engicoder/kroy360_usb/firmware/6x8_horizontal_lsb_1.h

#include <stdint.h>
#include <avr/pgmspace.h>

const uint8_t font[256][8] PROGMEM =
{
{0x00,0x00,0x00,0x00,0x00,0x00,0x00,0x00},	// 0x00
{0x70,0x88,0xD8,0x88,0xA8,0x88,0x70,0x00},	// 0x01
{0x70,0xF8,0xA8,0xF8,0x88,0xF8,0x70,0x00},	// 0x02
{0x00,0x50,0xF8,0xF8,0xF8,0x70,0x20,0x00},	// 0x03
{0x00,0x20,0x70,0xF8,0xF8,0x70,0x20,0x00},	// 0x04
{0x20,0x70,0x70,0x20,0xF8,0xF8,0x20,0x00},	// 0x05
{0x00,0x20,0x70,0xF8,0xF8,0x20,0x70,0x00},	// 0x06
{0x00,0x00,0x00,0x00,0x00,0x00,0x00,0x00},	// 0x07
{0x00,0x00,0x00,0x00,0x00,0x00,0x00,0x00},	// 0x08
{0x00,0x00,0x00,0x00,0x00,0x00,0x00,0x00},	// 0x09
{0x00,0x00,0x00,0x00,0x00,0x00,0x00,0x00},	// 0x0A
{0x00,0xE0,0xC0,0xB0,0x48,0x48,0x30,0x00},	// 0x0B
{0x70,0x88,0x88,0x70,0x20,0x70,0x20,0x00},	// 0x0C
{0x00,0x00,0x00,0x00,0x00,0x00,0x00,0x00},	// 0x0D
{0xC0,0xB0,0xD0,0xB0,0xD0,0xD8,0x18,0x00},	// 0x0E
{0x00,0xA8,0x70,0xD8,0x70,0xA8,0x00,0x00},	// 0x0F
{0x10,0x30,0x70,0xF0,0x70,0x30,0x10,0x00},	// 0x10
{0x40,0x60,0x70,0x78,0x70,0x60,0x40,0x00},	// 0x11
{0x20,0x70,0xF8,0x20,0xF8,0x70,0x20,0x00},	// 0x12
{0x50,0x50,0x50,0x50,0x50,0x00,0x50,0x00},	// 0x13
{0xF0,0xA8,0xA8,0xB0,0xA0,0xA0,0xA0,0x00},	// 0x14
{0x70,0x88,0x30,0x50,0x60,0x88,0x70,0x00},	// 0x15
{0x00,0x00,0x00,0x00,0x00,0x78,0x78,0x00},	// 0x16
{0x20,0x70,0xF8,0x20,0xF8,0x70,0x20,0x70},	// 0x17
{0x20,0x70,0xF8,0x20,0x20,0x20,0x20,0x00},	// 0x18
{0x20,0x20,0x20,0x20,0xF8,0x70,0x20,0x00},	// 0x19
{0x00,0x20,0x60,0xF8,0x60,0x20,0x00,0x00},	// 0x1A
{0x00,0x20,0x30,0xF8,0x30,0x20,0x00,0x00},	// 0x1B
{0x00,0x00,0x00,0x08,0x08,0x08,0xF8,0x00},	// 0x1C
{0x00,0x50,0x50,0xF8,0x50,0x50,0x00,0x00},	// 0x1D
{0x20,0x20,0x70,0x70,0xF8,0xF8,0x00,0x00},	// 0x1E
{0xF8,0xF8,0x70,0x70,0x20,0x20,0x00,0x00},	// 0x1F
{0x00,0x00,0x00,0x00,0x00,0x00,0x00,0x00},	// 0x20
{0x20,0x70,0x70,0x20,0x20,0x00,0x20,0x00},	// 0x21
{0xD8,0xD8,0x48,0x00,0x00,0x00,0x00,0x00},	// 0x22
{0x00,0x50,0xF8,0x50,0x50,0xF8,0x50,0x00},	// 0x23
{0x10,0x70,0x08,0x30,0x40,0x38,0x20,0x00},	// 0x24
{0x98,0x98,0x40,0x20,0x10,0xC8,0xC8,0x00},	// 0x25
{0x10,0x28,0x28,0x10,0xA8,0x48,0xB0,0x00},	// 0x26
{0x30,0x30,0x10,0x00,0x00,0x00,0x00,0x00},	// 0x27
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
};
