engicoder/kroy360_usb/firmware/config.h

/*
Copyright 2019 engicoder
*/

#ifndef CONFIG_H
#define CONFIG_H


/* USB Device descriptor parameter */
#define VENDOR_ID       0xFEED
#define PRODUCT_ID      0x6060
#define DEVICE_VER      0x0001
#define MANUFACTURER    Kroy
#define PRODUCT         360
#define DESCRIPTION     Kory 360 converter

/* key matrix size */
#define MATRIX_ROWS 5
#define MATRIX_COLS 16

#define USB_MAX_POWER_CONSUMPTION 500



/* define if matrix has ghost */
#define MATRIX_HAS_GHOST

/* Set 0 if debouncing isn't needed */
#define DEBOUNCE    10

/* Mechanical locking support. Use KC_LCAP, KC_LNUM or KC_LSCR instead in keymap */
//#define LOCKING_SUPPORT_ENABLE
/* Locking resynchronize hack */
//#define LOCKING_RESYNC_ENABLE

/* key combination for command */
/*
#define IS_COMMAND() ( \
    keyboard_report->mods == (MOD_BIT(KC_LSHIFT) | MOD_BIT(KC_RSHIFT)) \
)
*/


#endif
